Sadrita404/Node-Zero/Images/16.png

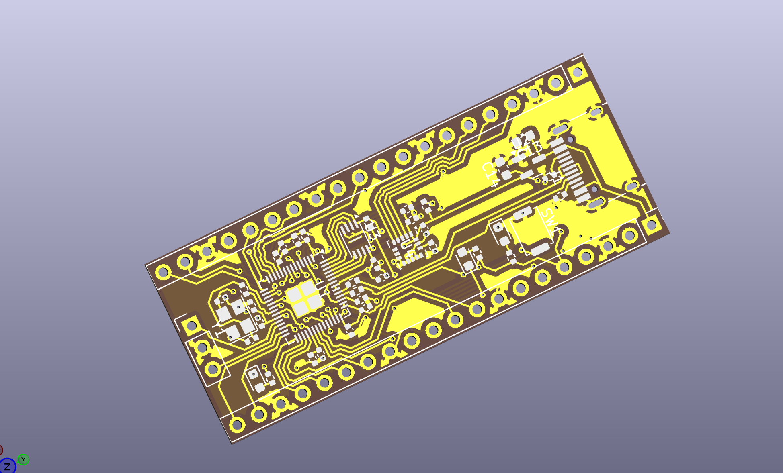
Images/16.png
