Sadrita404/Node-Zero/Images/1.png

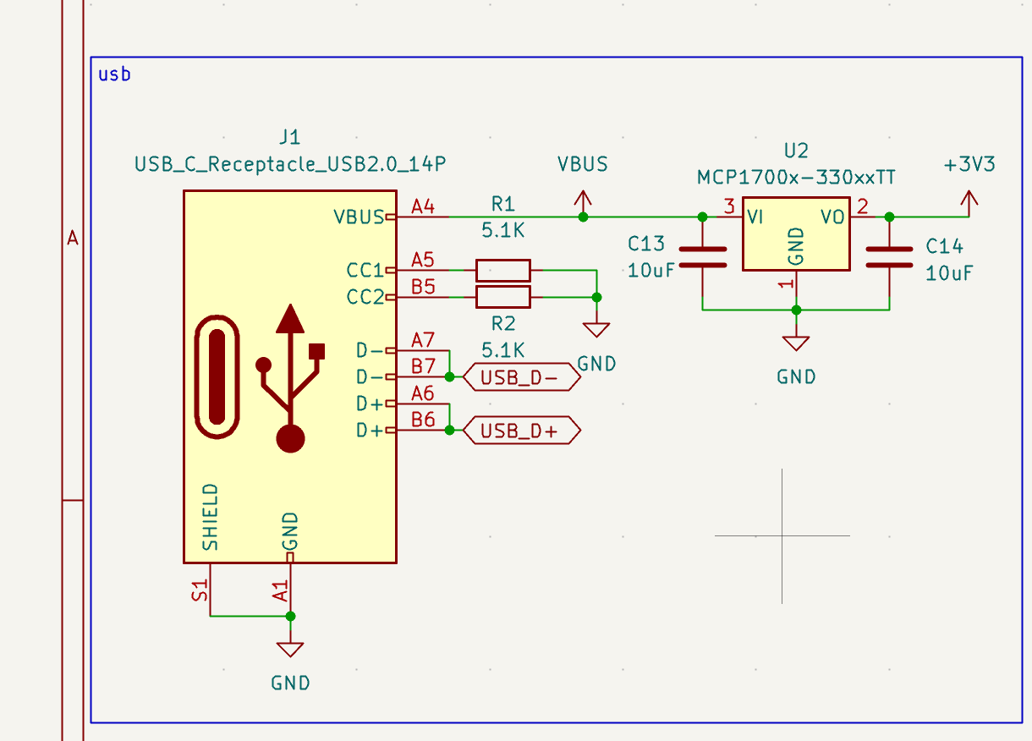
Images/1.png
