Sadrita404/Node-Zero/Images/2.png

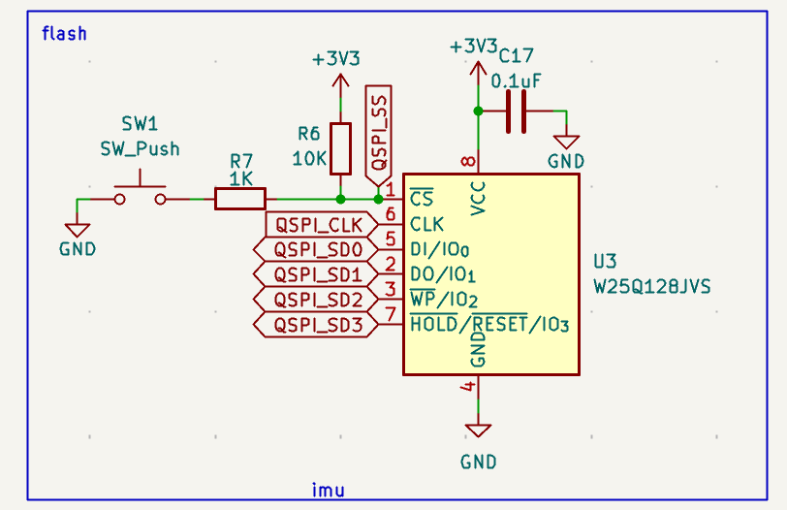
Images/2.png
