Sadrita404/Node-Zero/Images/3.png

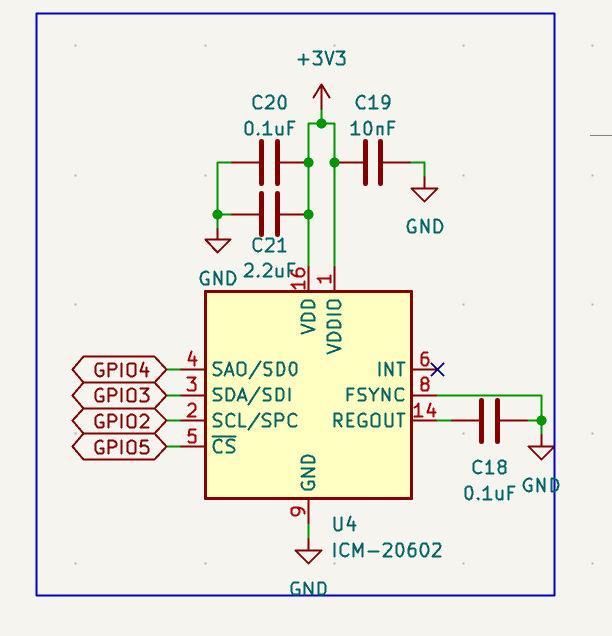
Images/3.png
