Sadrita404/Node-Zero/Images/4.png

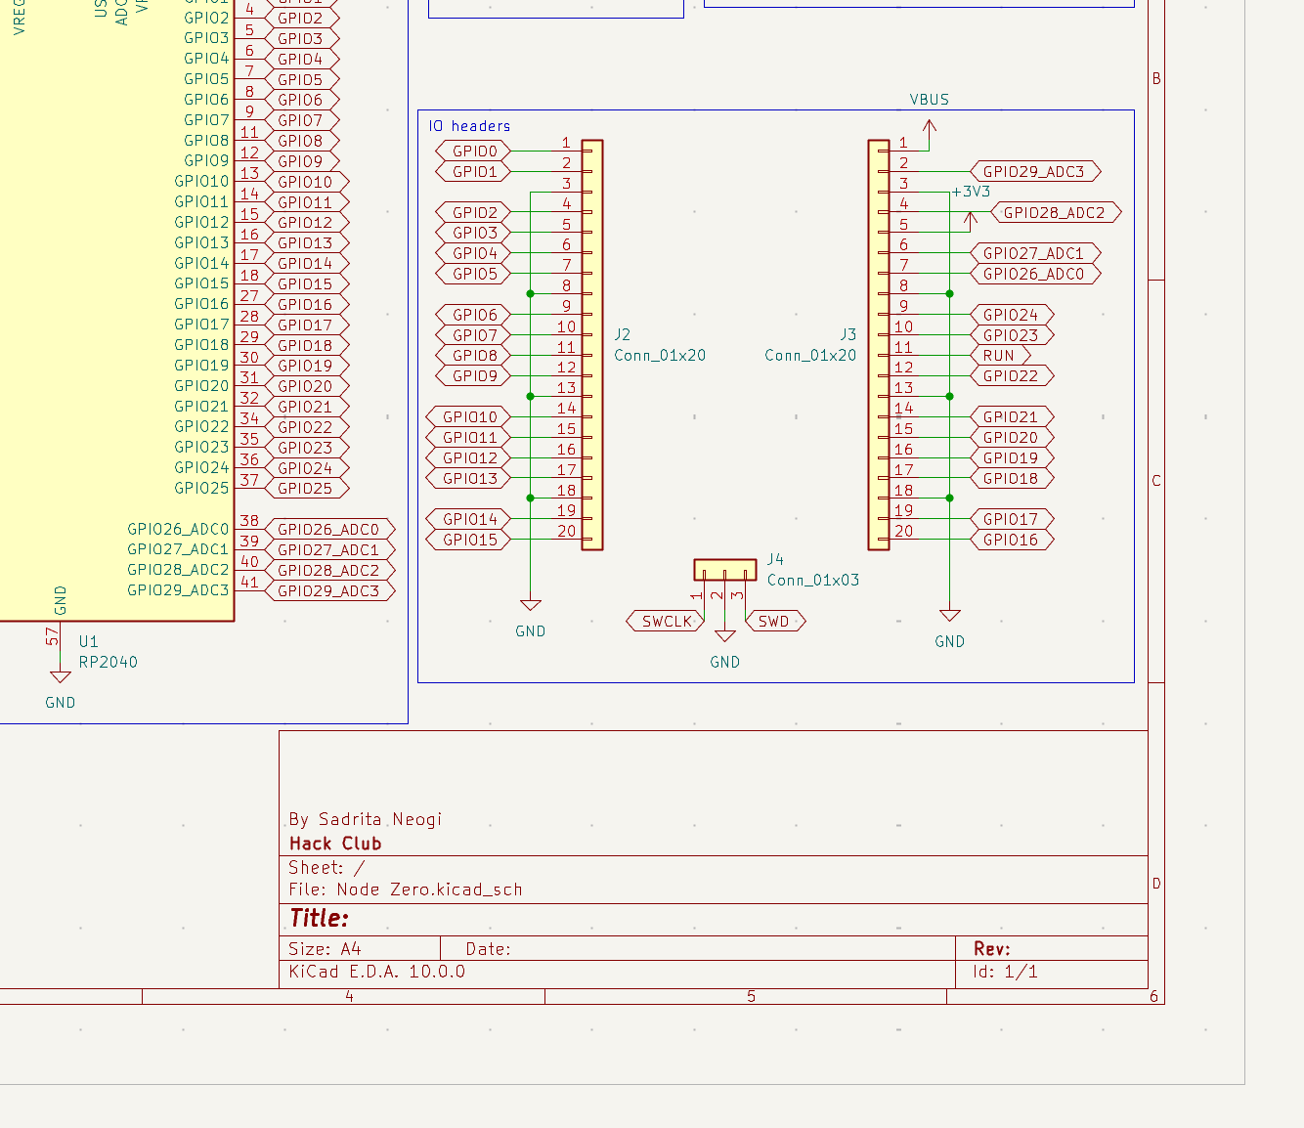
Images/4.png
