Sadrita404/Node-Zero/Images/5.png

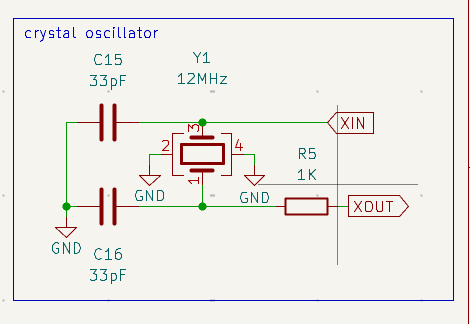
Images/5.png
