Sadrita404/Node-Zero/Images/6.png

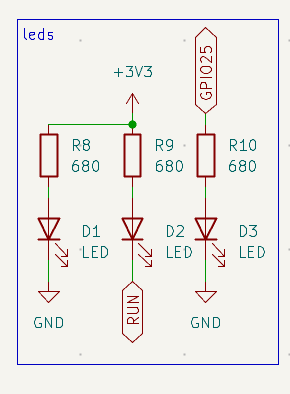
Images/6.png
