Sadrita404/Node-Zero/Images/7.png

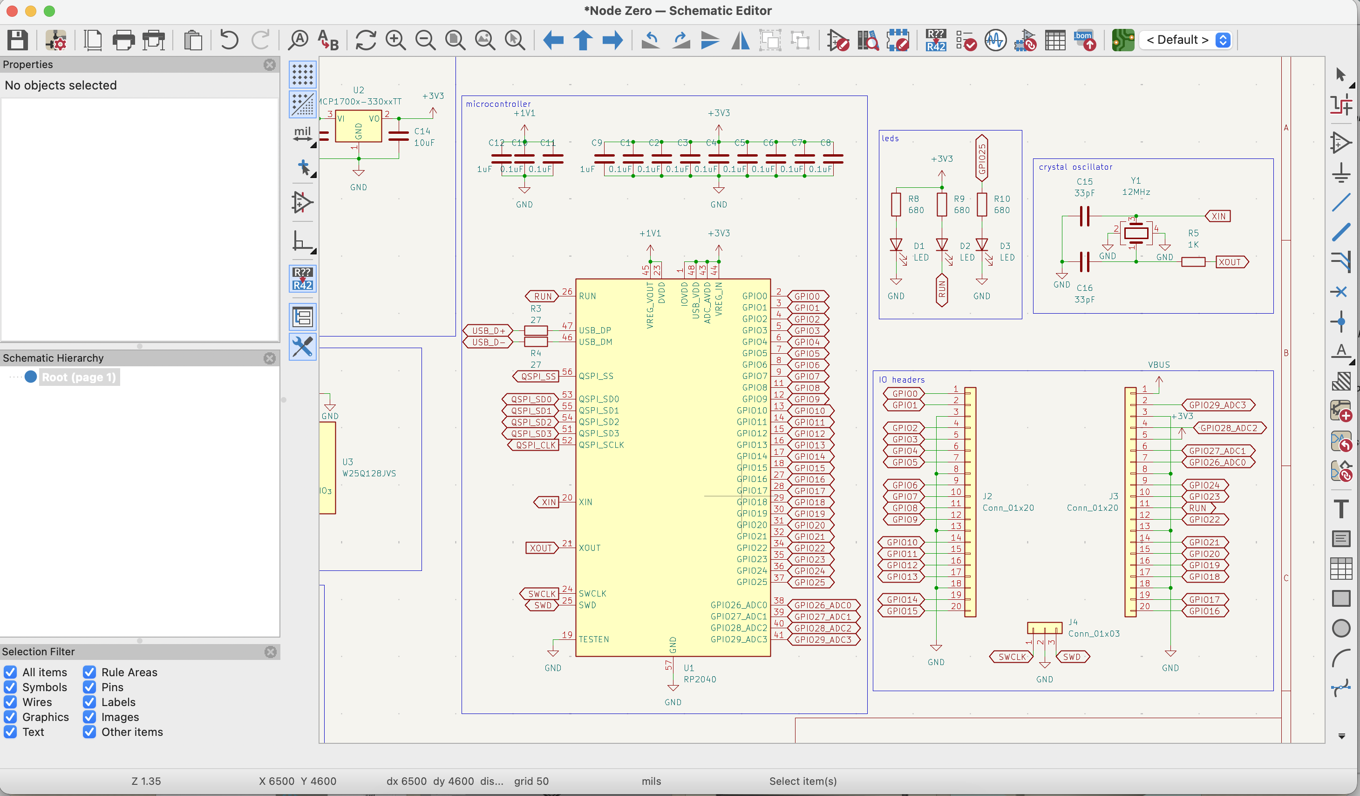
Images/7.png
