Sadrita404/Node-Zero/Images/8.png

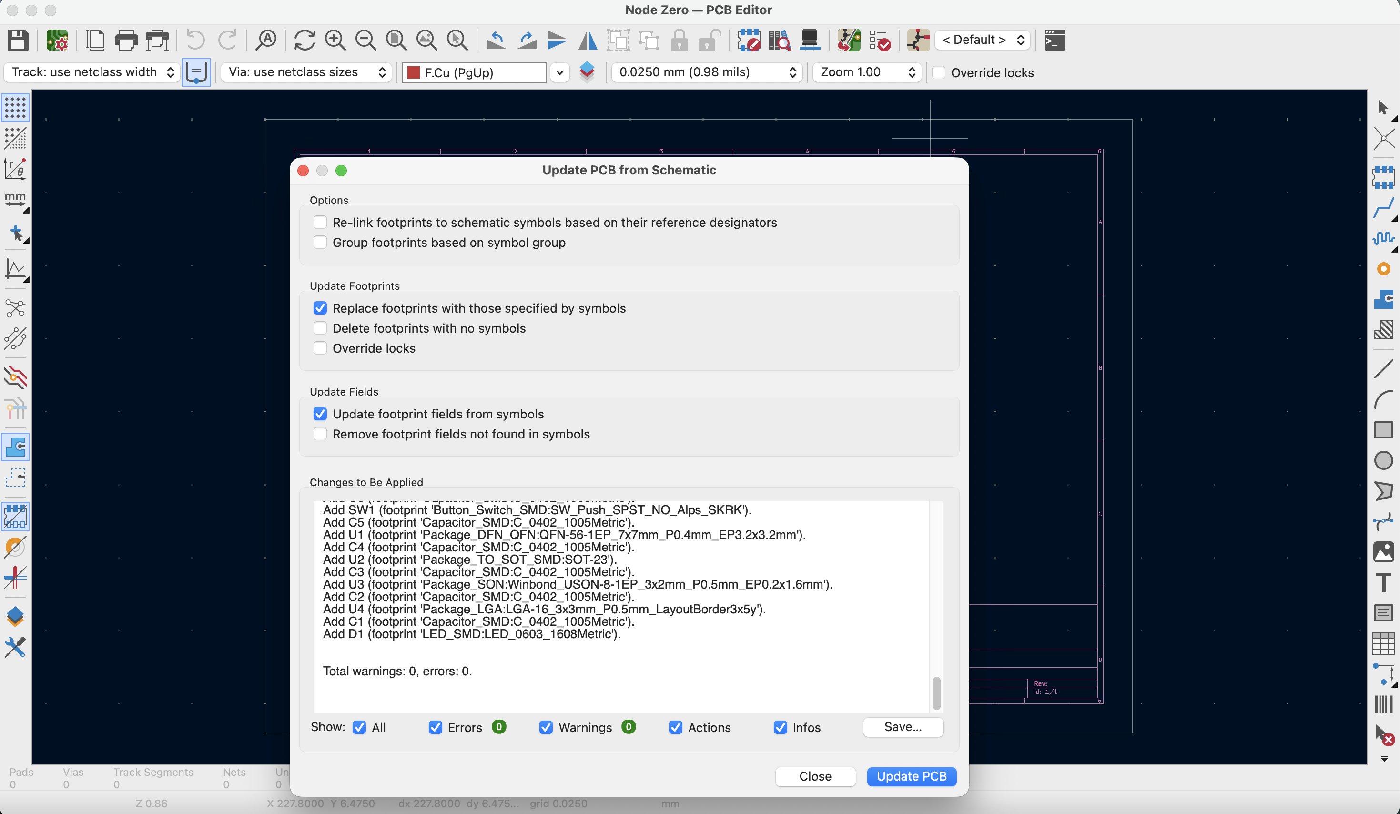
Images/8.png
