Sadrita404/Node-Zero/Images/9.png

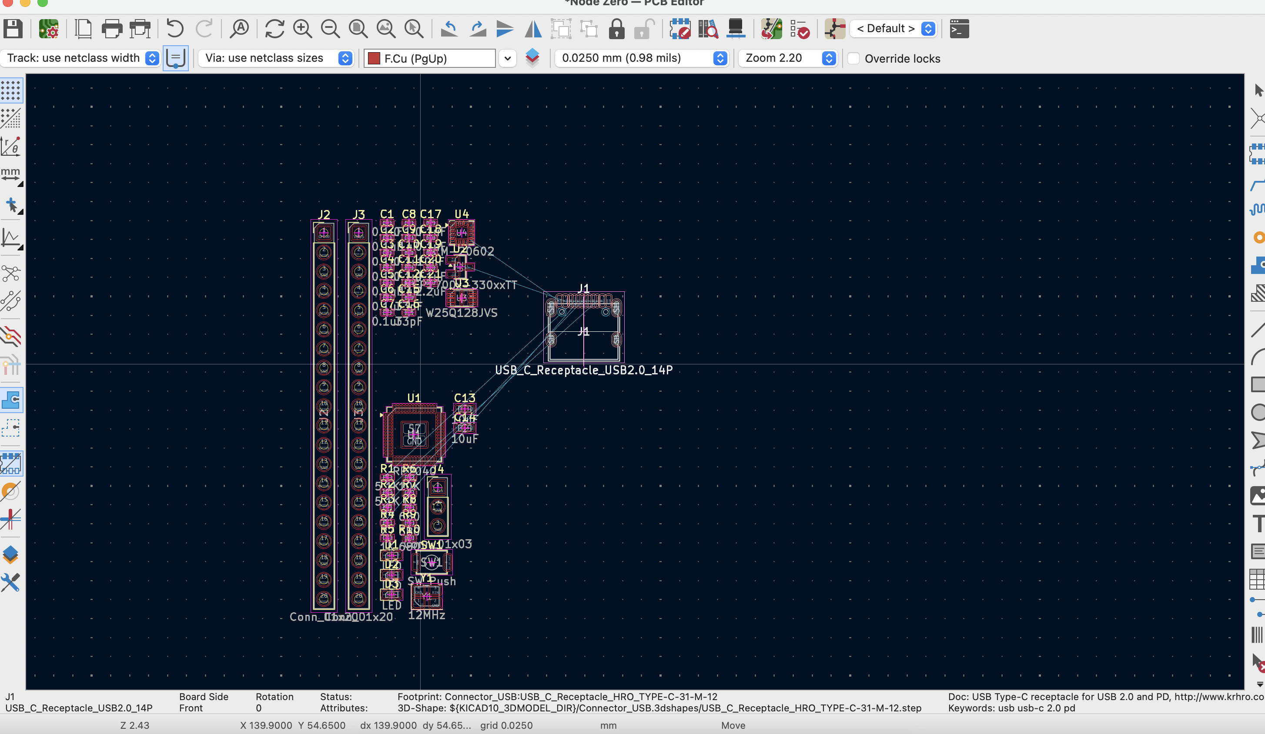
Images/9.png
