Sadrita404/Node-Zero/Images/11.png

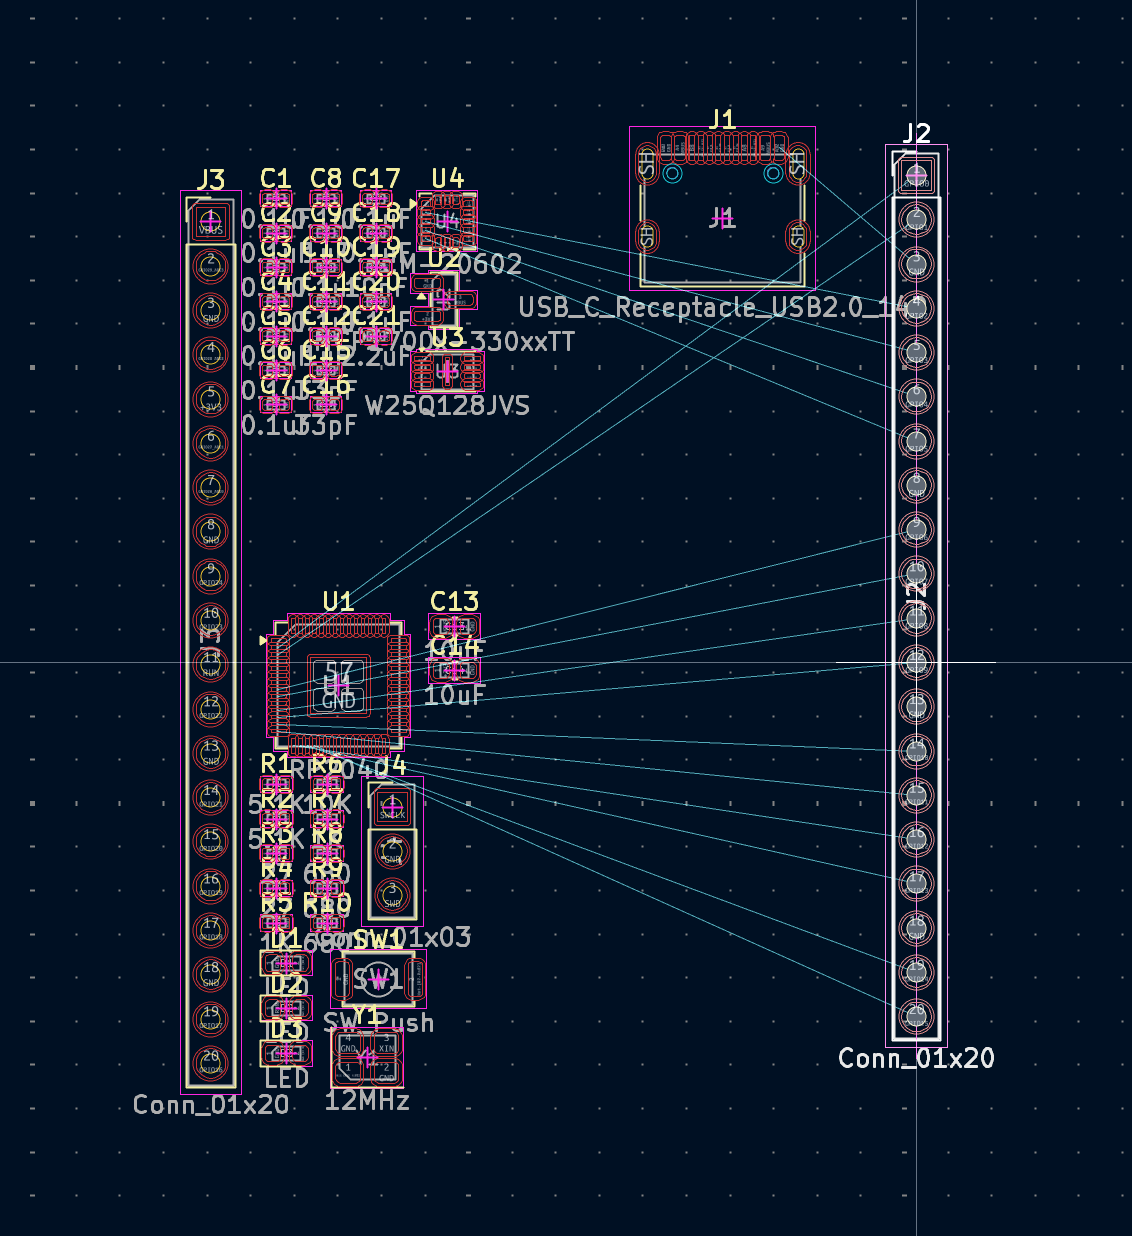
Images/11.png
