Sadrita404/Node-Zero/Images/12.png

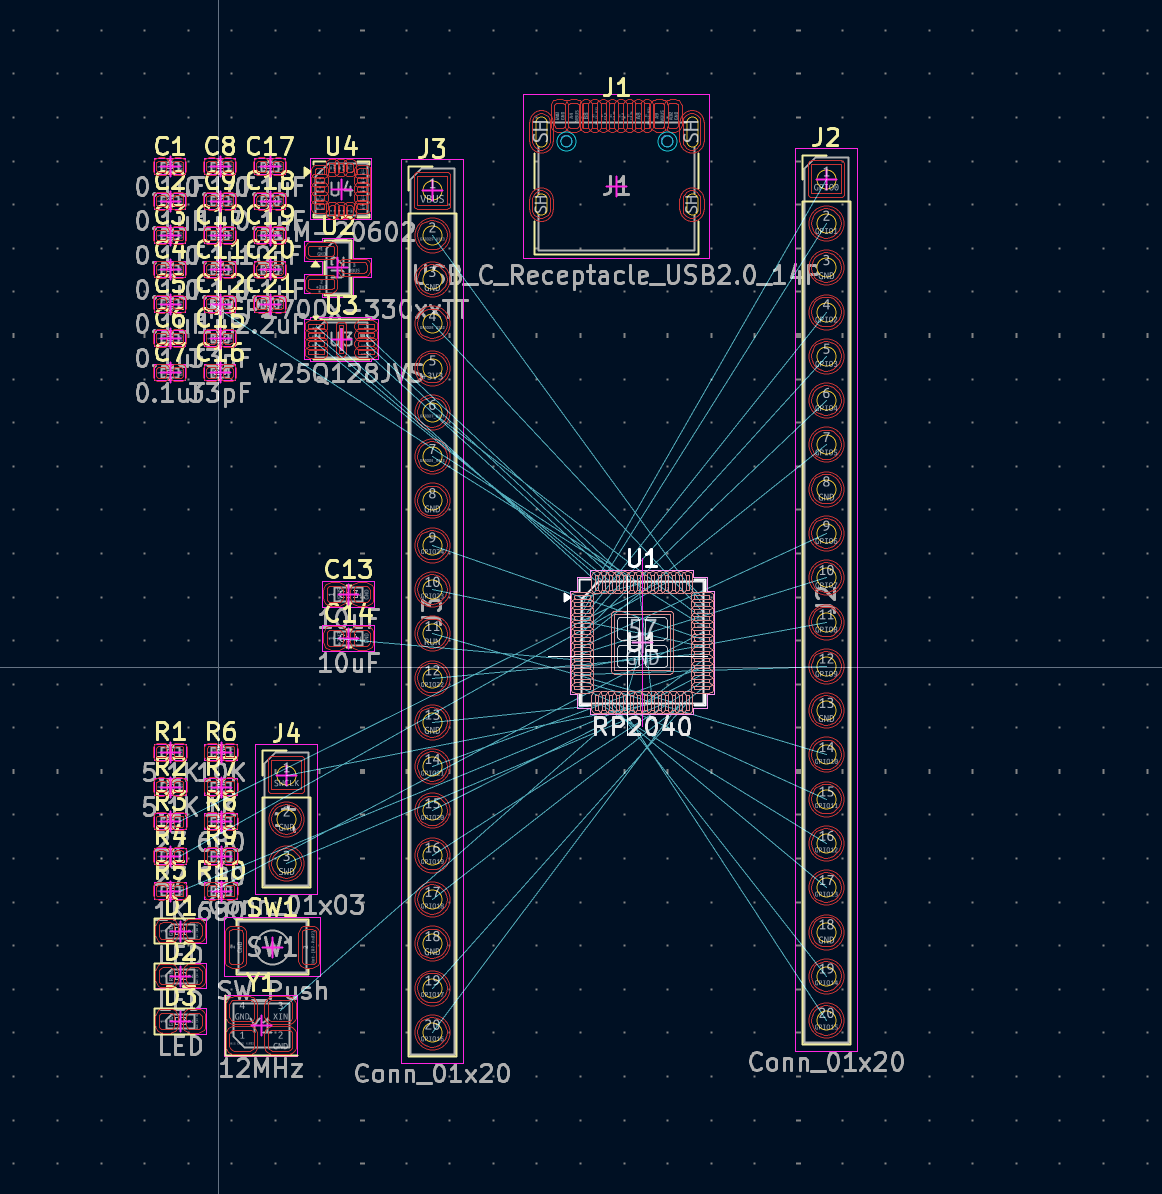
Images/12.png
