Sadrita404/Node-Zero/Images/13.png

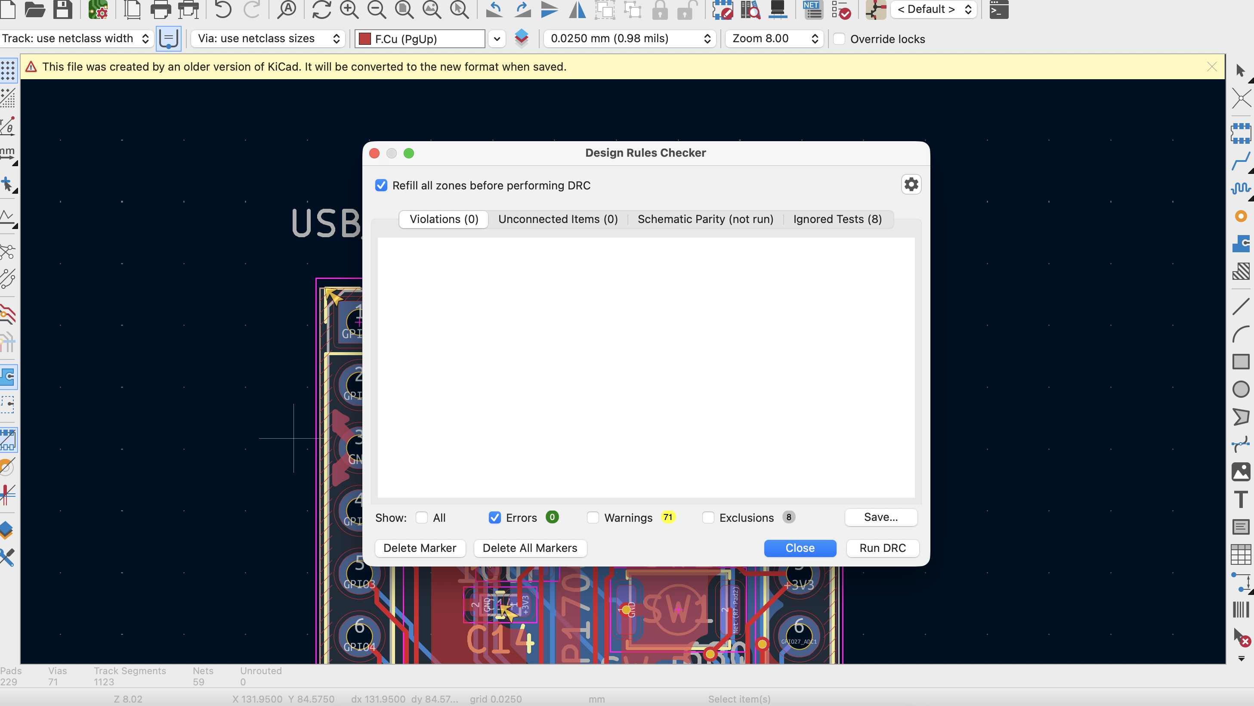
Images/13.png
