Sadrita404/Node-Zero/Images/14.png

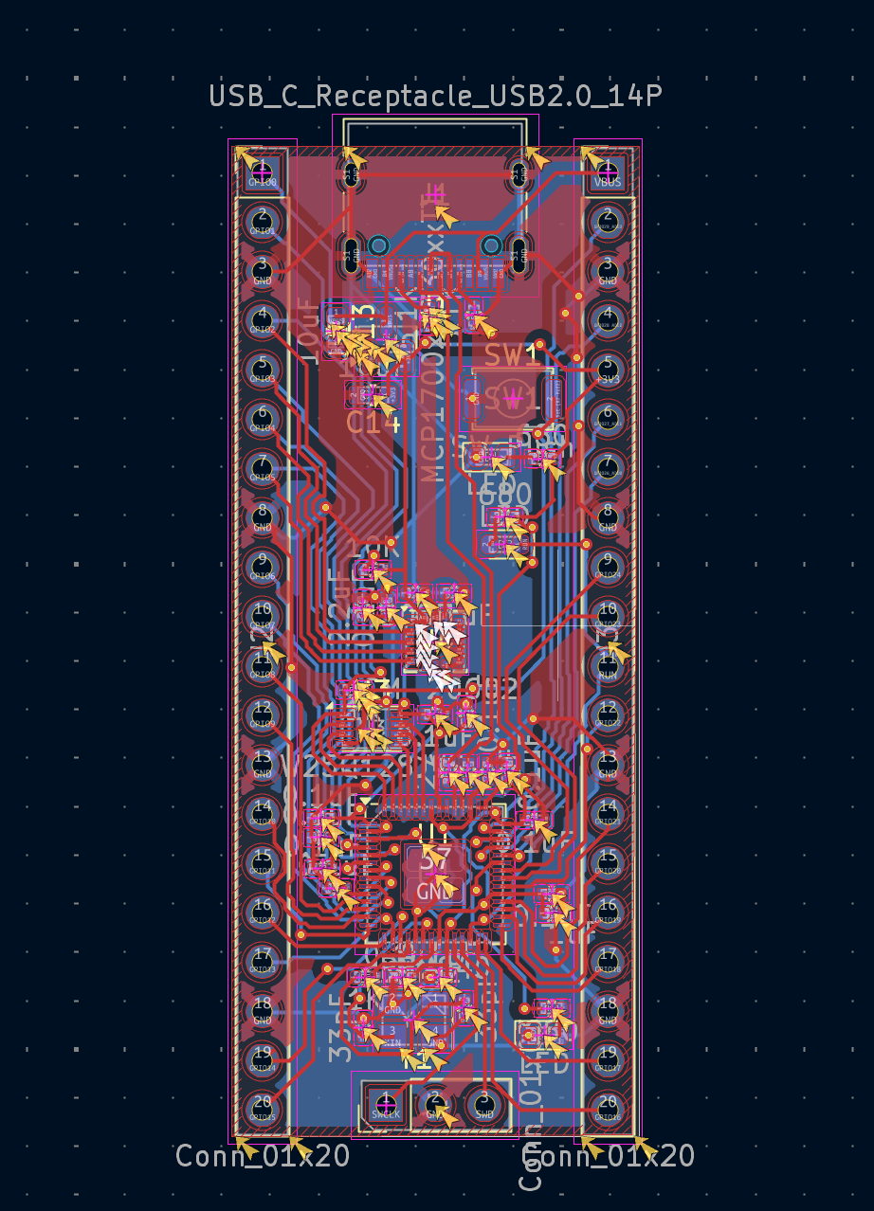
Images/14.png
