Sadrita404/Node-Zero/Images/15.png

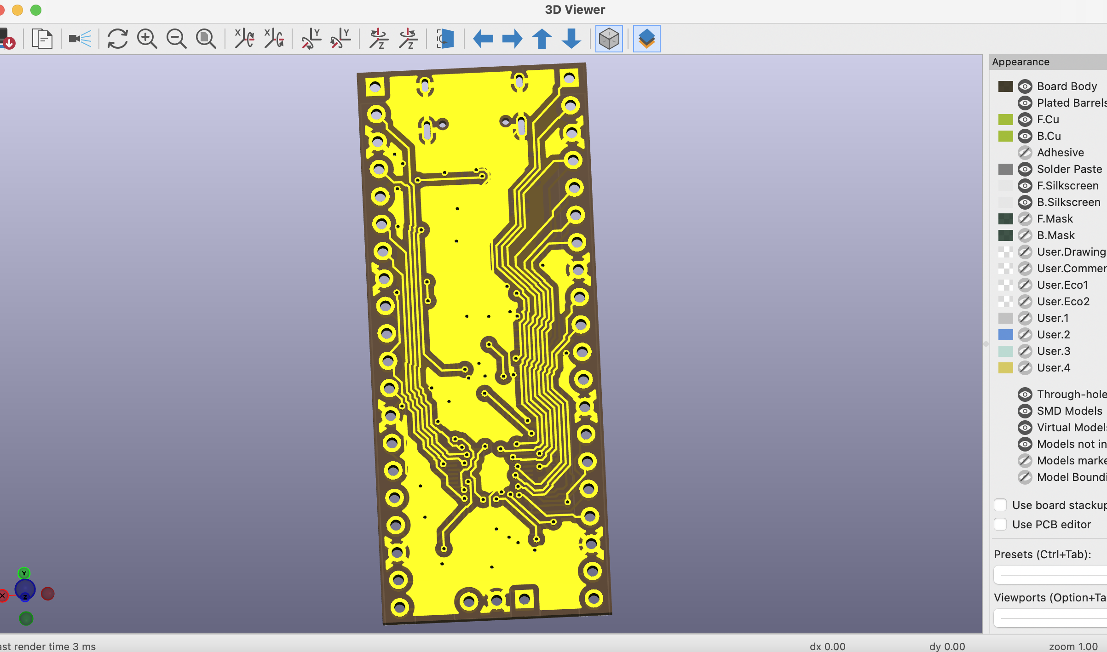
Images/15.png
