Sadrita404/Node-Zero/Images/17.png

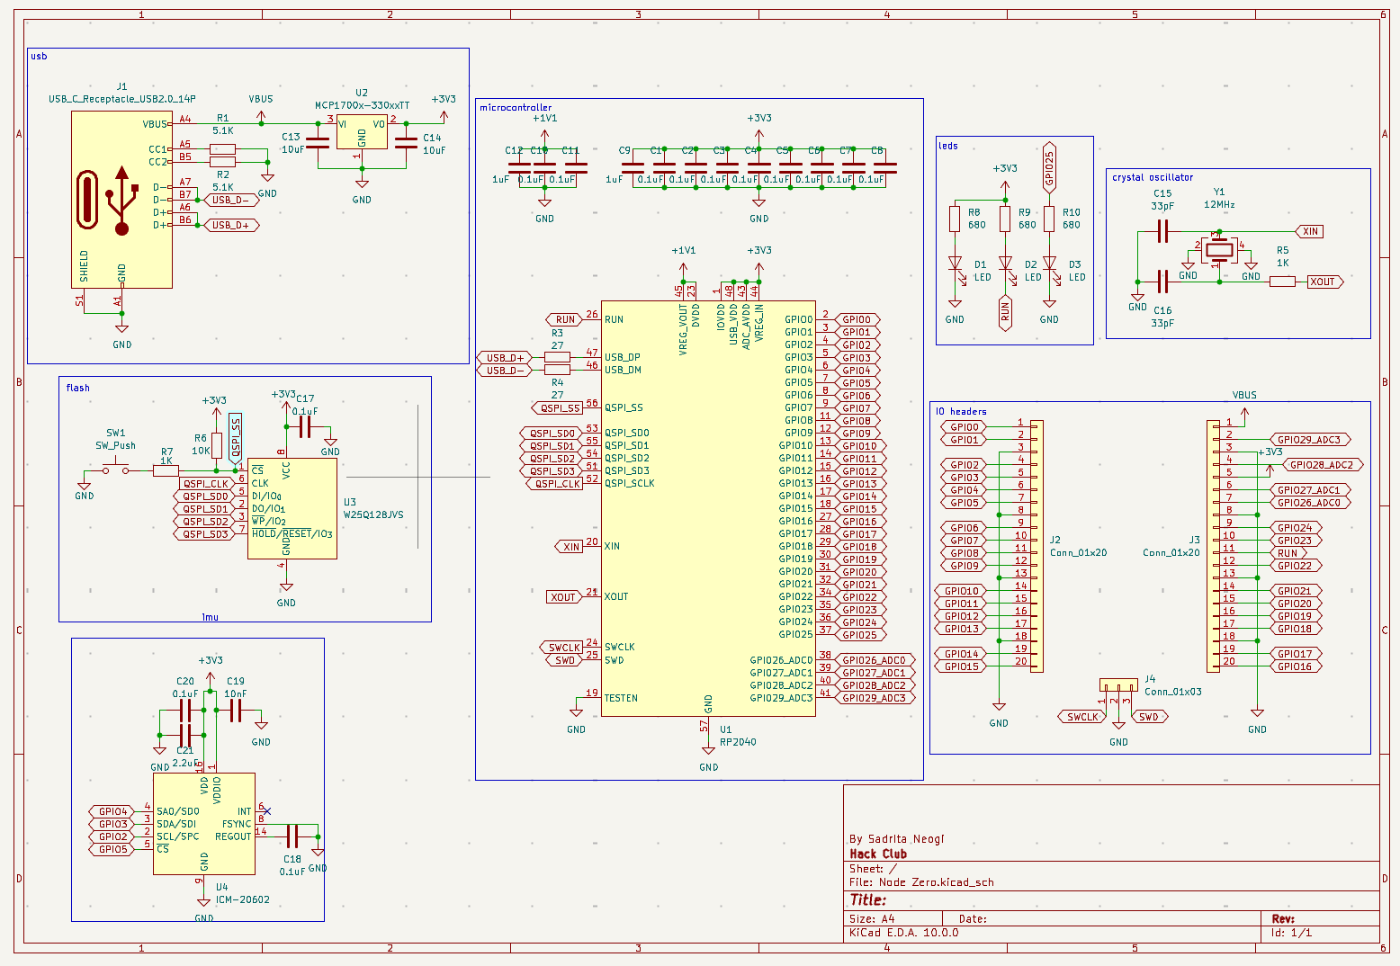
Images/17.png
