Sadrita404/Node-Zero/Images/18.png

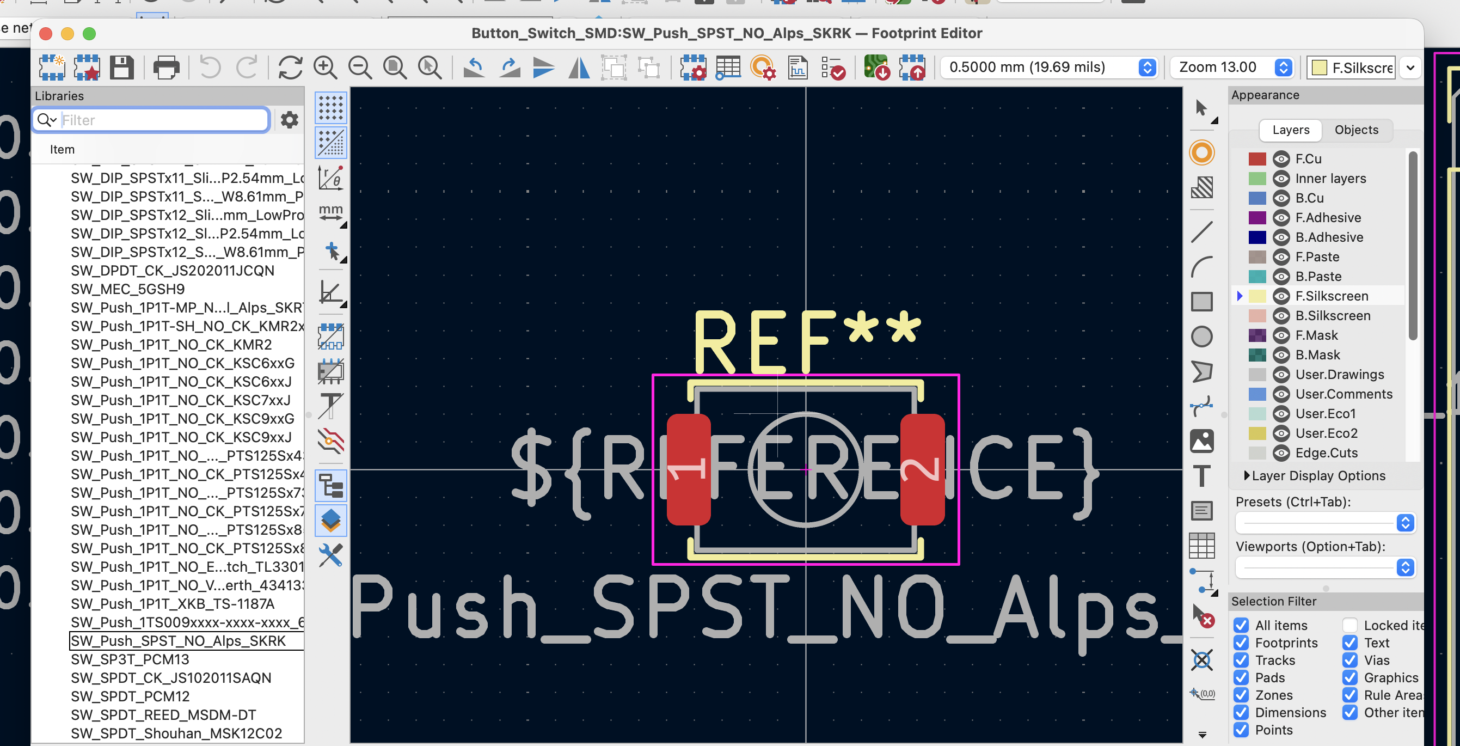
Images/18.png
