Sadrita404/Node-Zero/Images/19.png

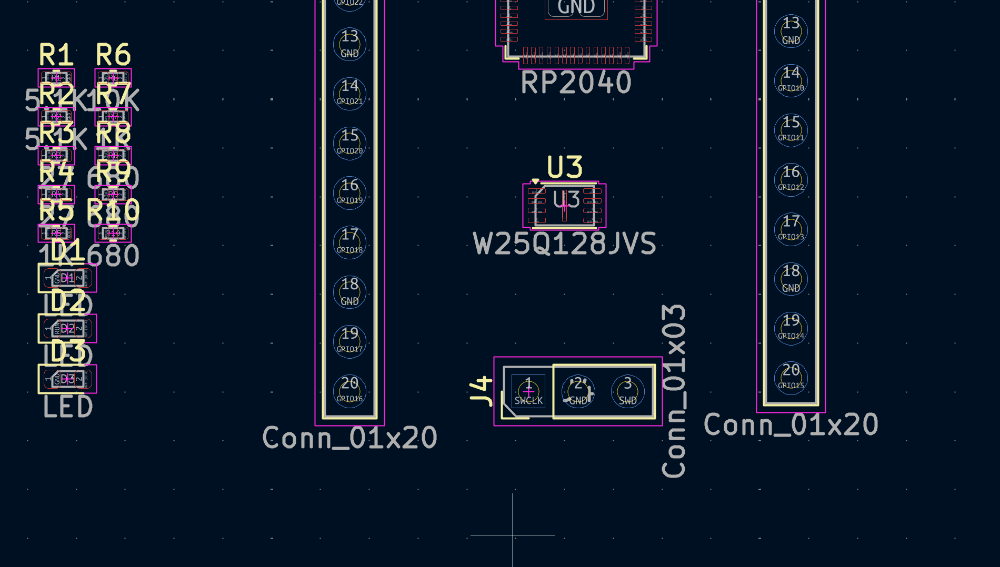
Images/19.png
