Sadrita404/Node-Zero/Images/20.png

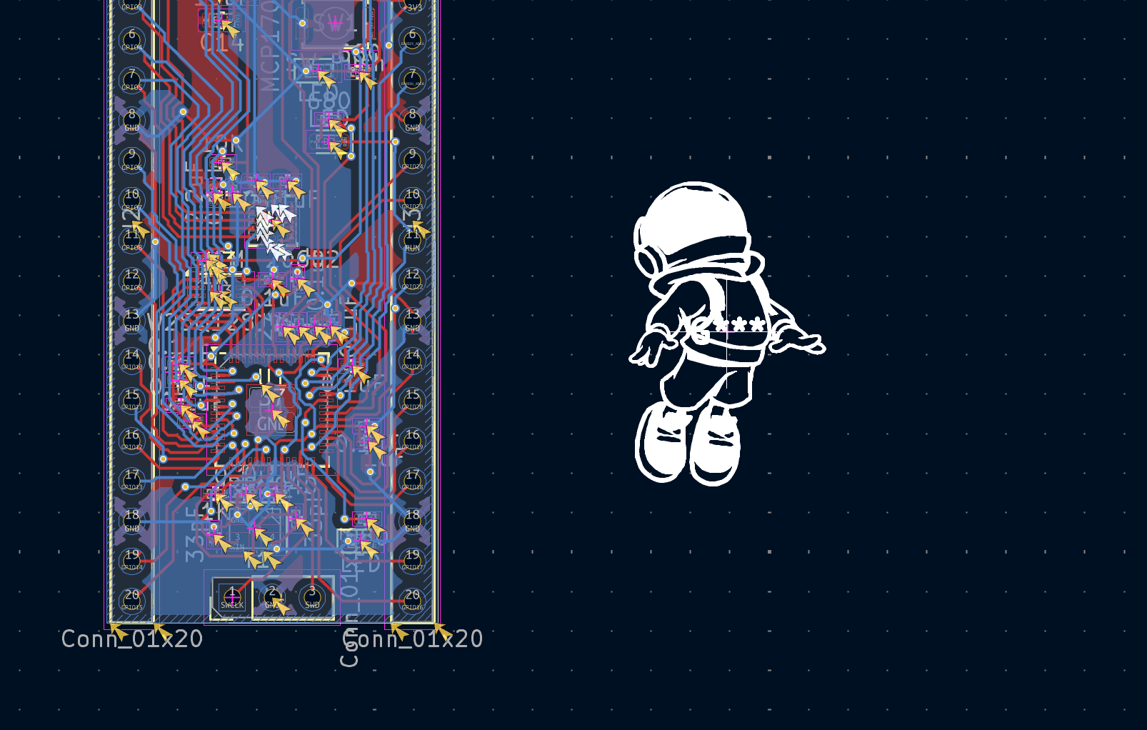
Images/20.png
