Sadrita404/Node-Zero/Images/21.png

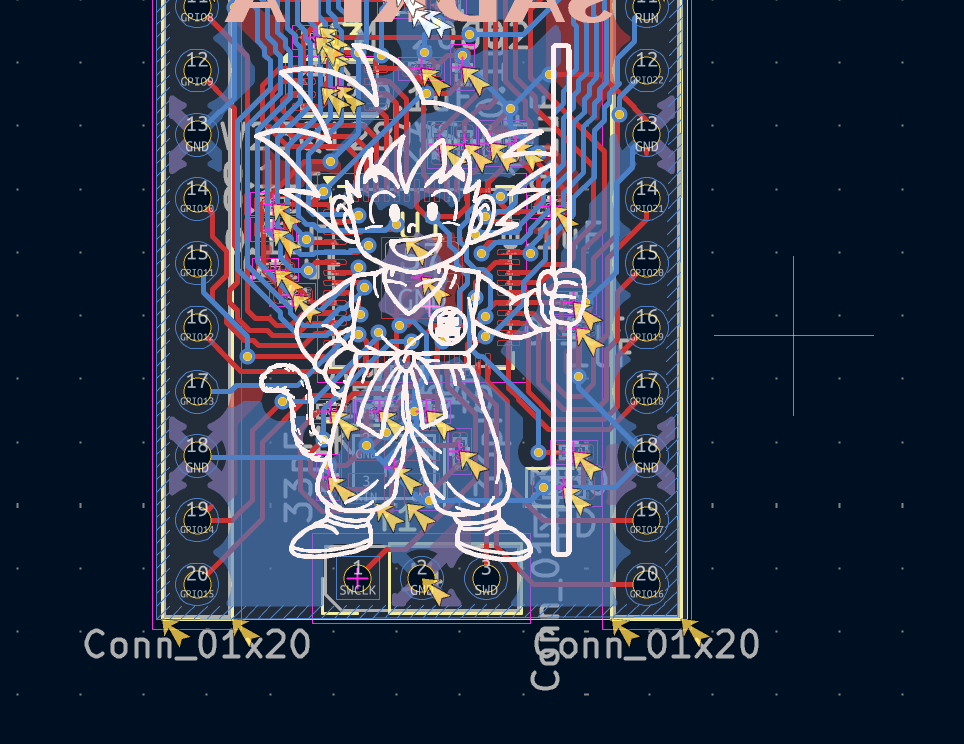
Images/21.png
