Sadrita404/Node-Zero/Images/23.png

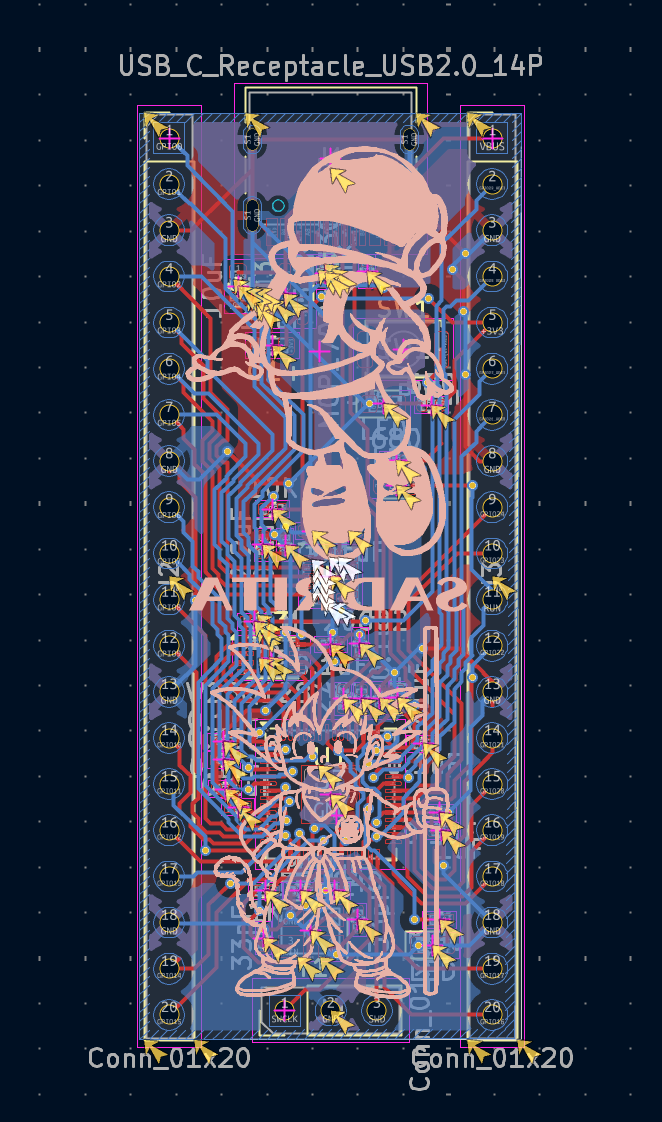
Images/23.png
