Sadrita404/Node-Zero/Images/24.png

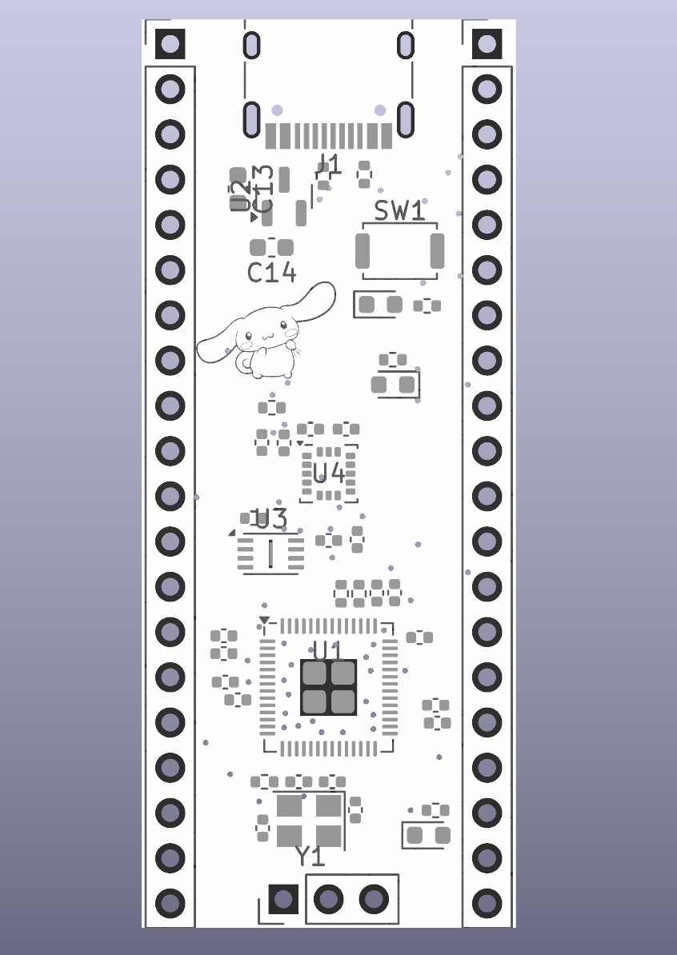
Images/24.png
