Sadrita404/Node-Zero/Images/25.png

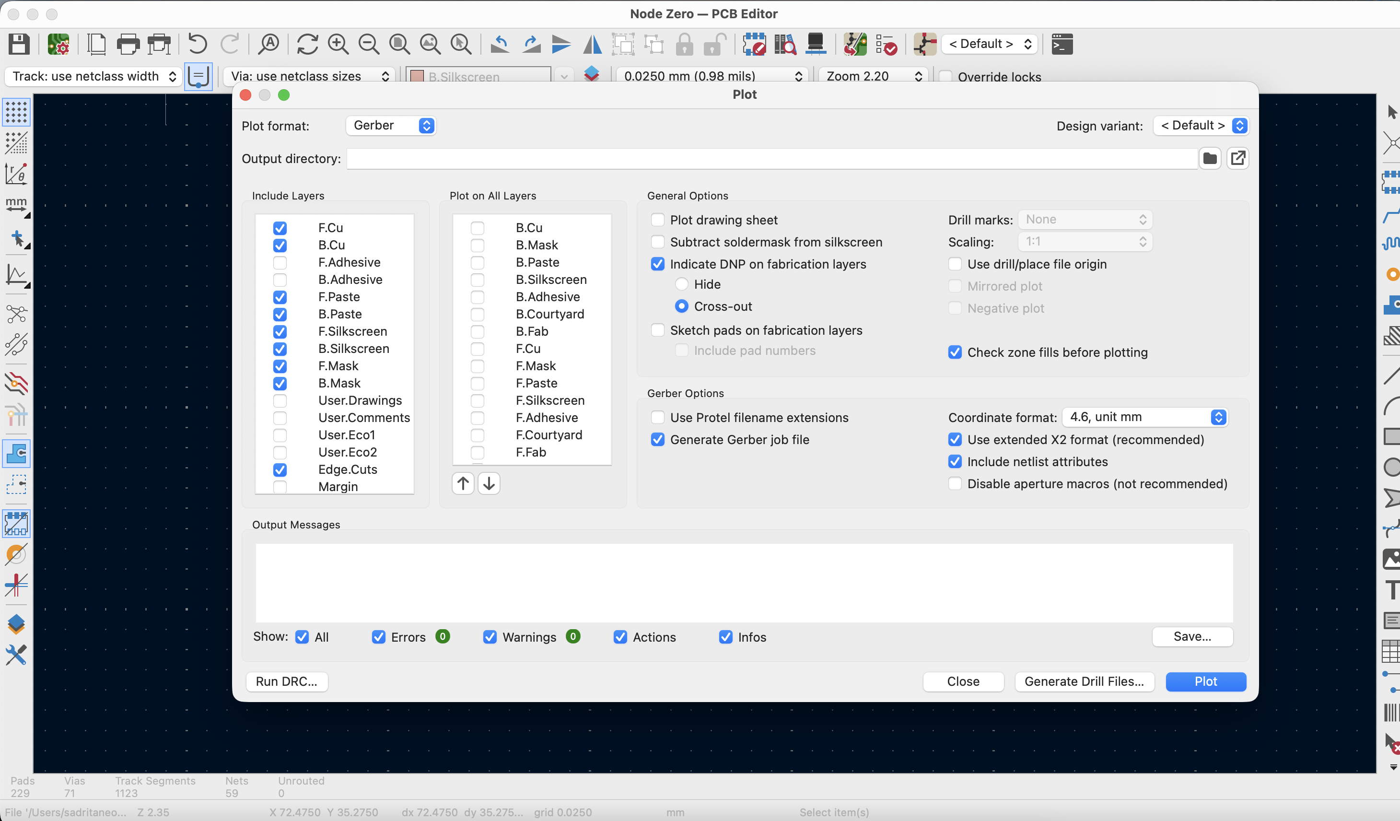
Images/25.png
