Sadrita404/Node-Zero/Images/26.png

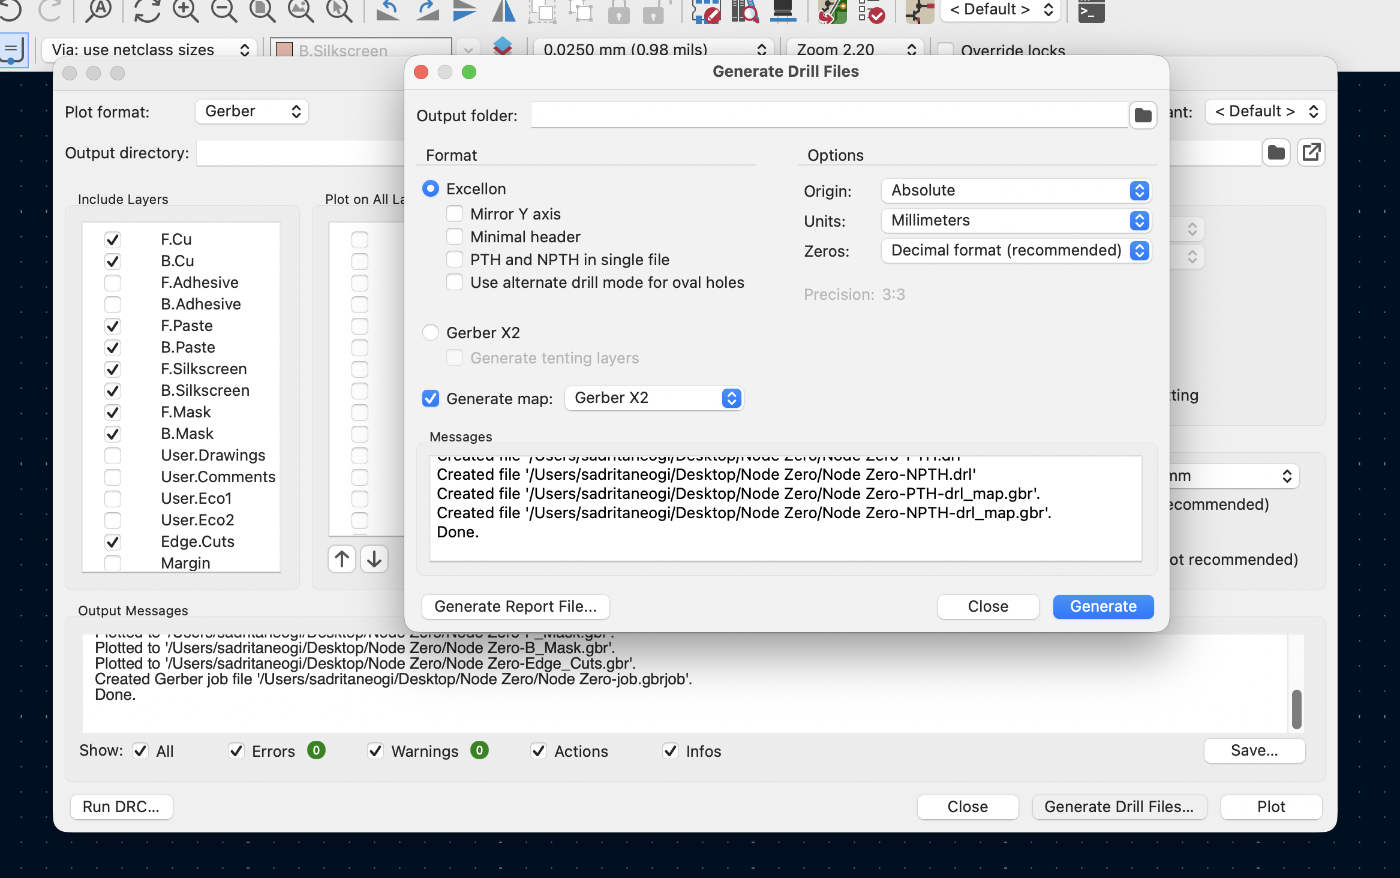
Images/26.png
