Sadrita404/Node-Zero/Images/27.png

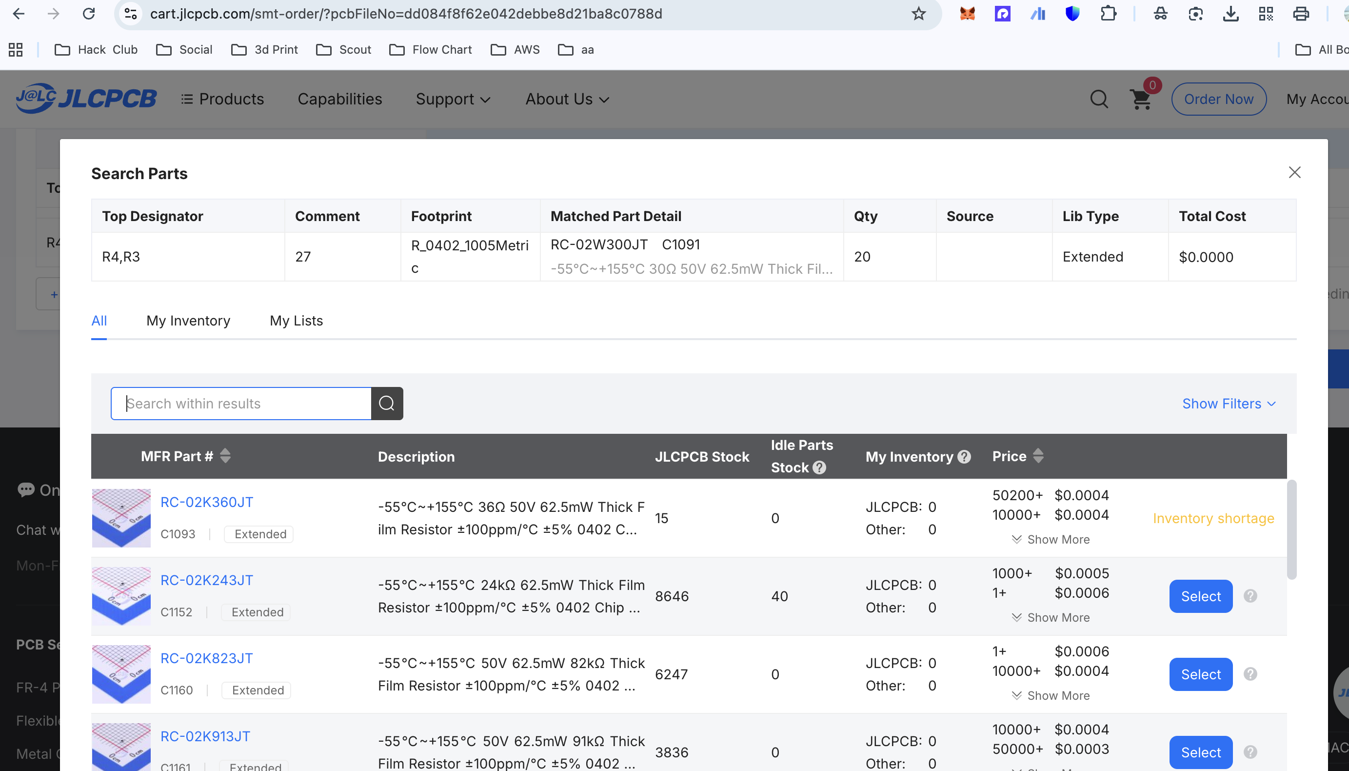
Images/27.png
