Sadrita404/Node-Zero/Images/28.png

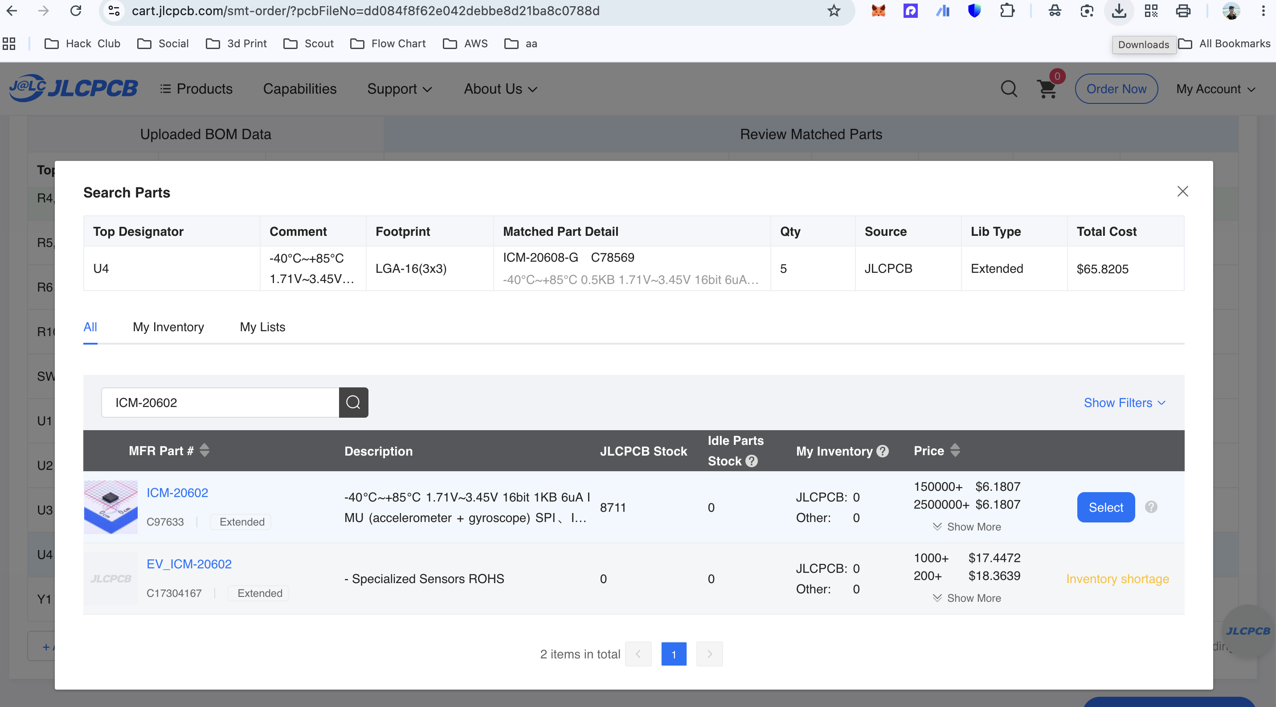
Images/28.png
