Sadrita404/Node-Zero/Images/29.png

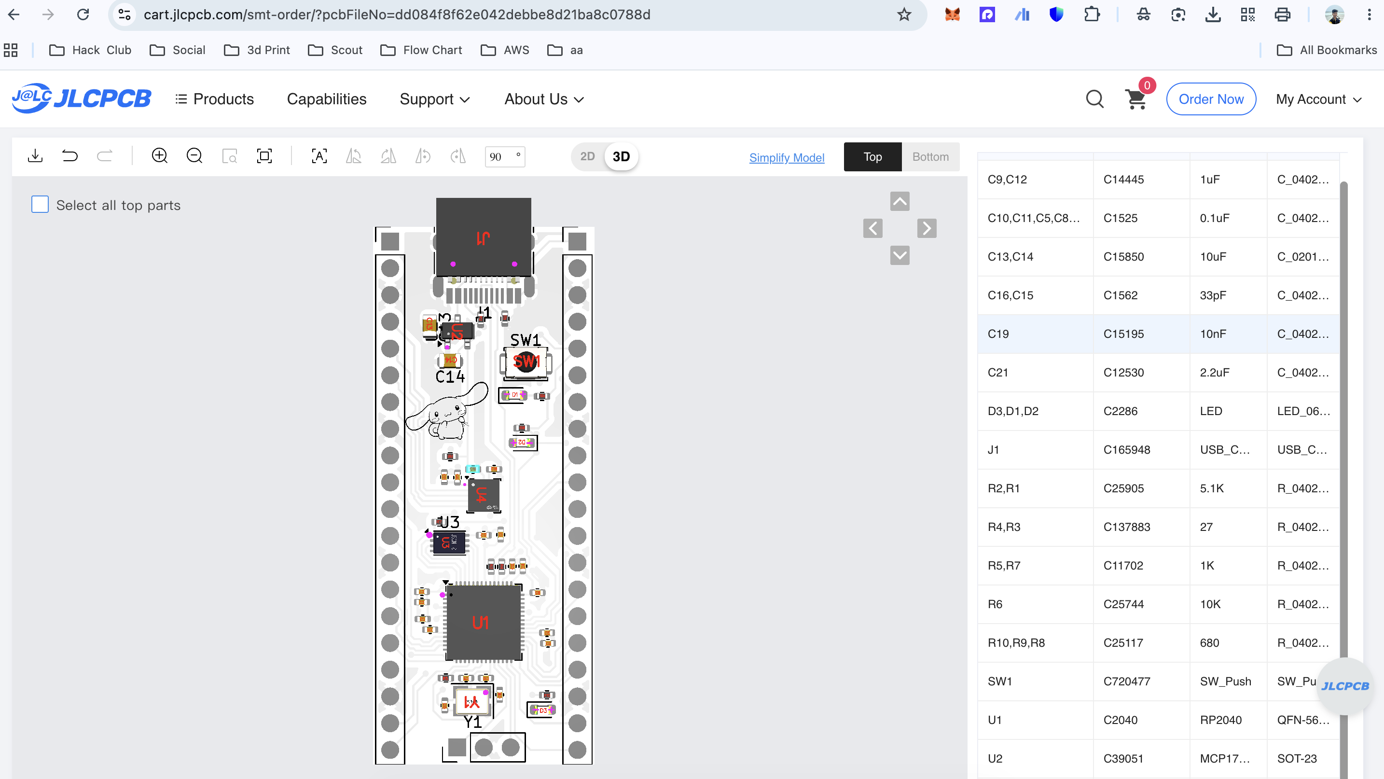
Images/29.png
