Sadrita404/Node-Zero/Images/30.png

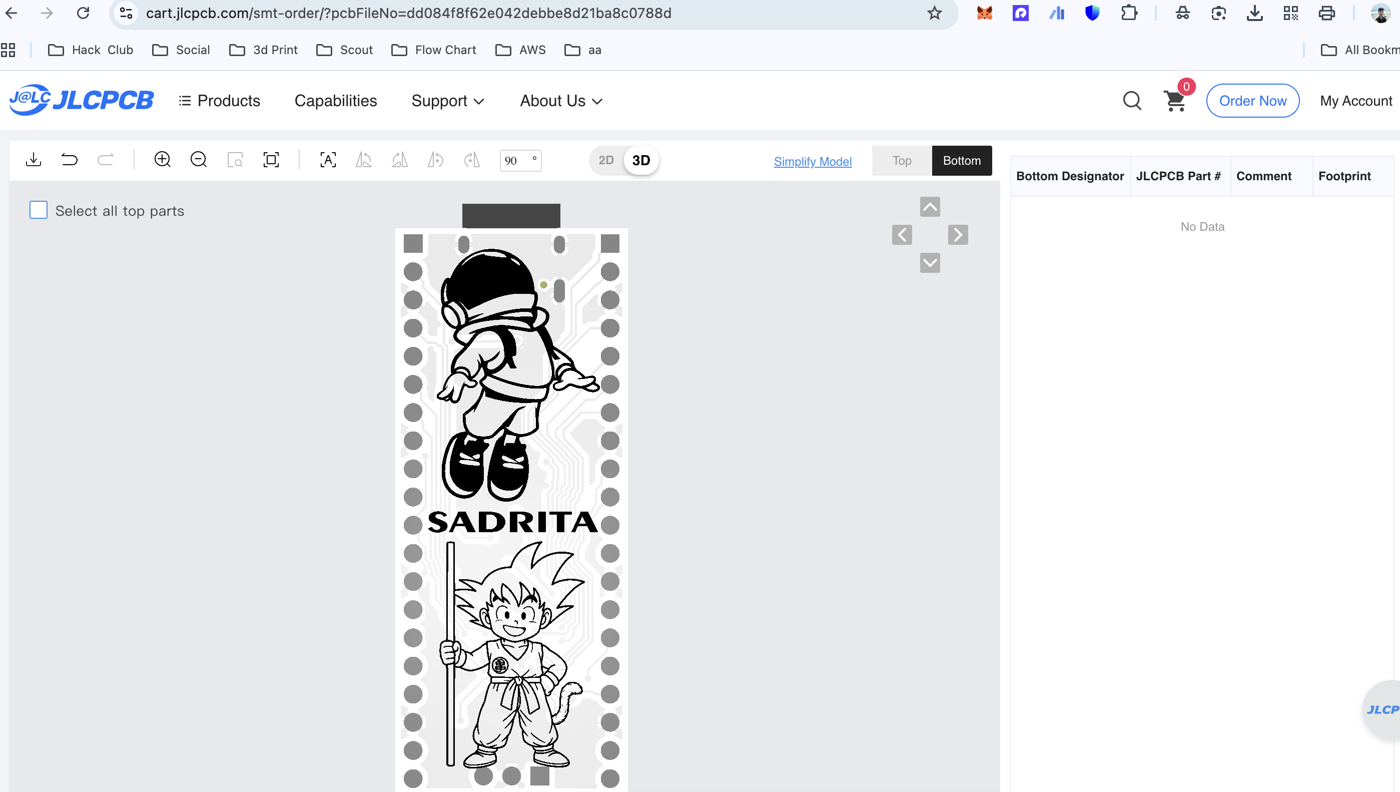
Images/30.png
