Sadrita404/Node-Zero/Images/31.png

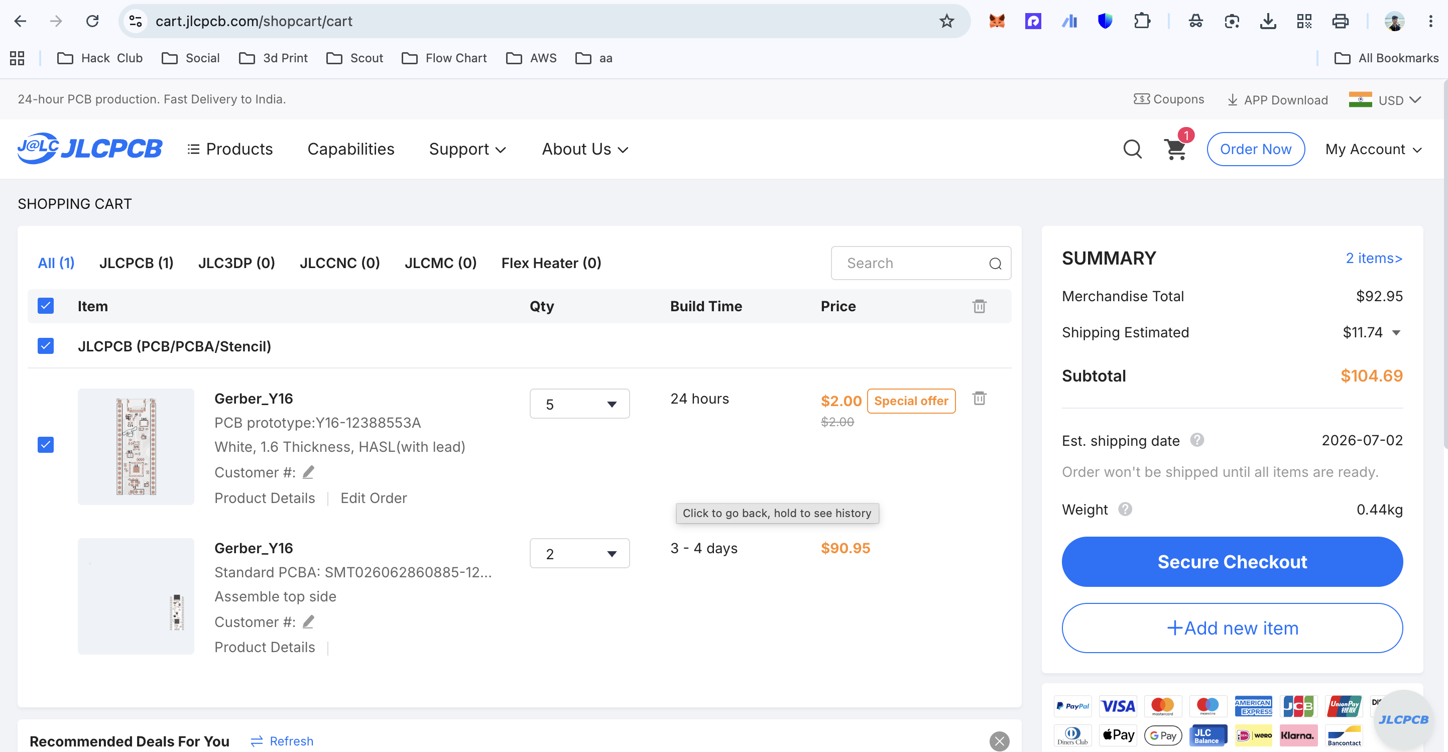
Images/31.png
